shreyadascoder2004/stm32-can-modbus-gateway/modbus_crc.c

/*
 * modbus_crc.c
 *
 *  Created on: 08-Aug-2026
 *      Author: shreya
 */


#include "modbus_crc.h"

uint16_t modbus_crc16(const uint8_t *buf, uint16_t len)
{
    uint16_t crc = 0xFFFF;

    for (uint16_t pos = 0; pos < len; pos++)
    {
        crc ^= (uint16_t)buf[pos];

        for (int i = 8; i != 0; i--)
        {
            if ((crc & 0x0001) != 0)
            {
                crc >>= 1;
                crc ^= 0xA001;
            }
            else
            {
                crc >>= 1;
            }
        }
    }
    return crc;
}
